petrm25/weather_station/3D models/Radiation_shield/STEP/Top_plate.step

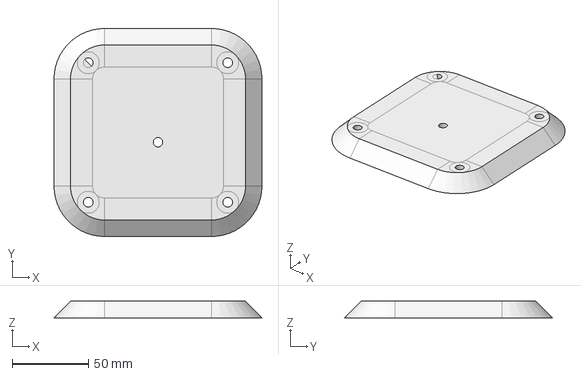
[picture p15: CAD file, 2021-05-24]
3D models/Radiation_shield/STEP/Top_plate.step
136.0 x 136.0 x 10.8 mm
