petrm25/weather_station/3D models/Protective_case/bottom.step

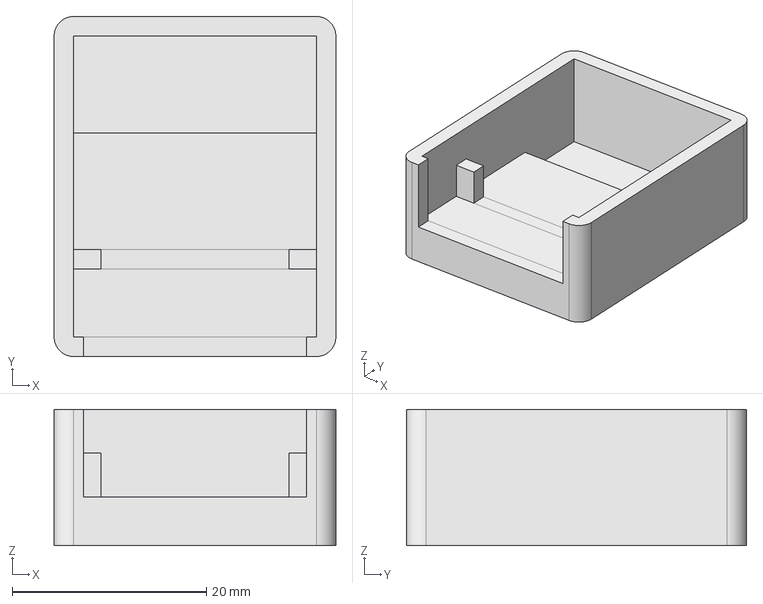
[picture p16: CAD file, 2021-05-24]
3D models/Protective_case/bottom.step
29.0 x 35.0 x 14.0 mm
