petrm25/weather_station/3D models/Radiation_shield/STEP/Top_cover_plate_UV_sensor.step

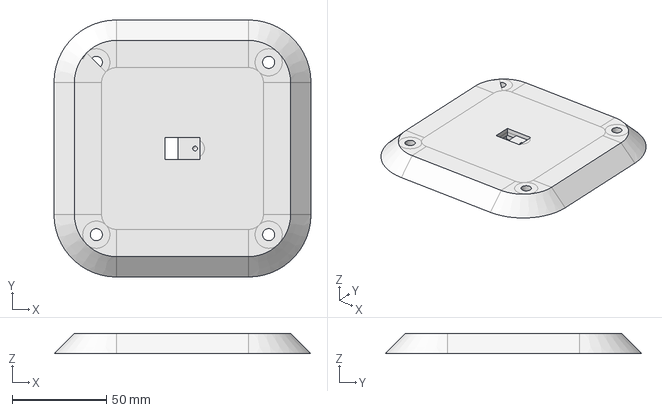
[picture p18: CAD file, 2021-05-24]
3D models/Radiation_shield/STEP/Top_cover_plate_UV_sensor.step
136.0 x 136.0 x 10.8 mm
