petrm25/weather_station/3D models/Radiation_shield/STEP/Cross.step

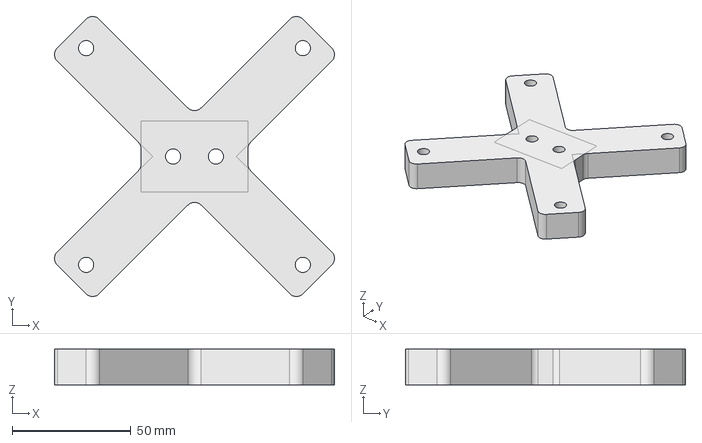
[picture p19: CAD file, 2021-05-24]
3D models/Radiation_shield/STEP/Cross.step
117.9 x 117.9 x 15.0 mm
