petrm25/weather_station/3D models/Radiation_shield/STEP/Bottom_cover_plate.step

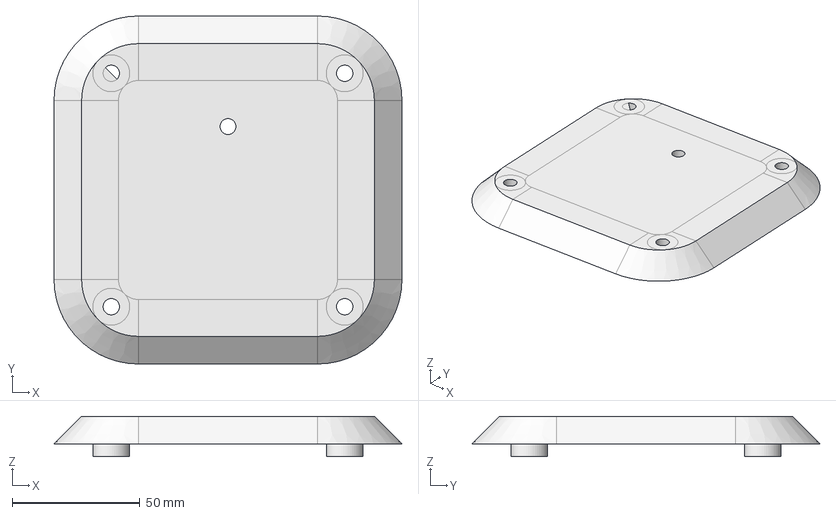
[picture p20: CAD file, 2021-05-24]
3D models/Radiation_shield/STEP/Bottom_cover_plate.step
136.0 x 136.0 x 15.8 mm
